Handterpret/Infrared_Analysis/Unit_test/Blink/Blink.ino

/*
  Blink

  Turns an LED on for one second, then off for one second, repeatedly.

  Most Arduinos have an on-board LED you can control. On the UNO, MEGA and ZERO
  it is attached to digital pin 13, on MKR1000 on pin 6. LED_BUILTIN is set to
  the correct LED pin independent of which board is used.
  If you want to know what pin the on-board LED is connected to on your Arduino
  model, check the Technical Specs of your board at:
  https://www.arduino.cc/en/Main/Products

  modified 8 May 2014
  by Scott Fitzgerald
  modified 2 Sep 2016
  by Arturo Guadalupi
  modified 8 Sep 2016
  by Colby Newman

  This example code is in the public domain.

  http://www.arduino.cc/en/Tutorial/Blink
*/
/*

Modified on 05/01/2020
By Florian Valade
for Handterpret

This example code has been modified from original version and is used to test 
Led Blinking and Photodiode.

Wiring to test on Arduino Nano :
Led on GRND and D2 (cathode)
Photodiode on 3.3V (cathode) and A0

Excpected output:
Open serial monitor and you should see a low value then a high value repeatedly

 */

int sensorValue = 0;  // variable to store the value coming from the sensor

// the setup function runs once when you press reset or power the board
void setup() {
  // initialize digital pin LED_BUILTIN as an output.
  pinMode(02, OUTPUT);
  Serial.begin(9600);
}

// the loop function runs over and over again forever
void loop() {
  digitalWrite(02, HIGH);   // turn the LED on (HIGH is the voltage level)
  sensorValue = analogRead(A0);
  Serial.println(sensorValue);
  delay(1000);                       // wait for a second
  digitalWrite(02, LOW);    // turn the LED off by making the voltage LOW
  sensorValue = analogRead(A0);
  Serial.println(sensorValue);
  delay(1000);                       // wait for a second
}
